aTinyShellScript/Polybar-Minibar-3D-Print-Files/Mods/MiniBar/[a]MB_Face_Plate.stl

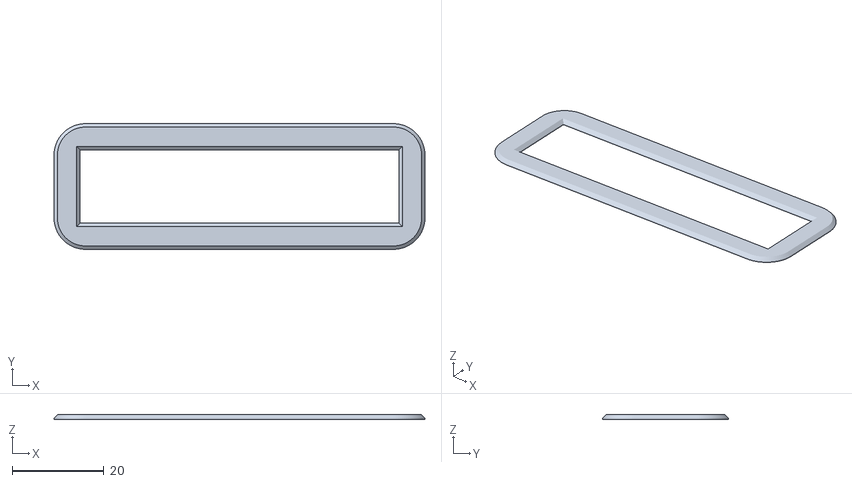
[picture p17: CAD file, 2022-12-14]
Mods/MiniBar/[a]MB_Face_Plate.stl
80.9 x 27.4 x 1.00
