aTinyShellScript/Polybar-Minibar-3D-Print-Files/Mods/PolyBar/[a]PB_Button_Board.stl

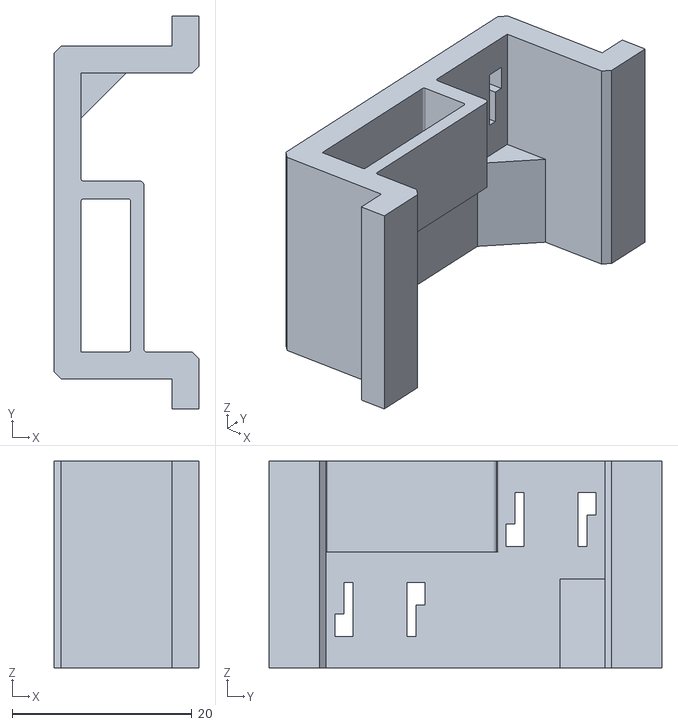
[picture p18: CAD file, 2022-12-14]
Mods/PolyBar/[a]PB_Button_Board.stl
16.1 x 43.7 x 23.0
