aTinyShellScript/Polybar-Minibar-3D-Print-Files/Mods/MiniBar/MB_Case_Top.stl

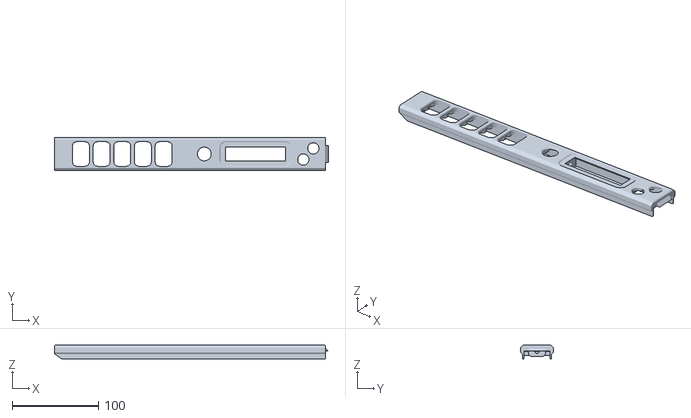
[picture p19: CAD file, 2022-12-14]
Mods/MiniBar/MB_Case_Top.stl
318.4 x 38.0 x 15.8
