aTinyShellScript/Polybar-Minibar-3D-Print-Files/Mods/PolyBar/[a]Strum_Swivel_Retainer_[x2].stl

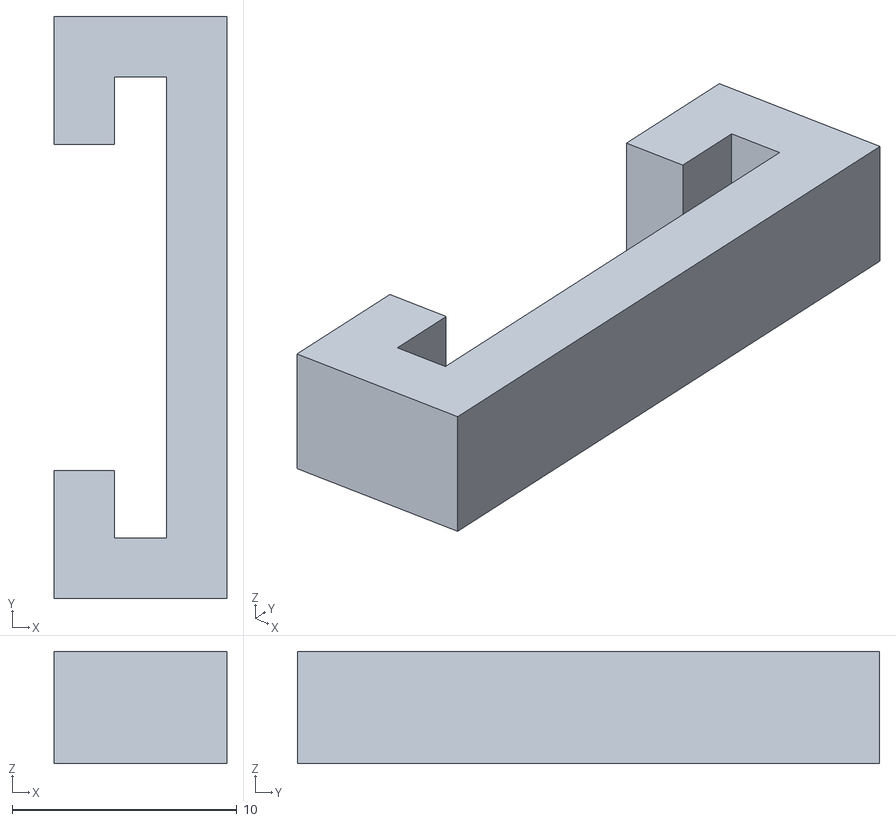
[picture p20: CAD file, 2022-12-14]
Mods/PolyBar/[a]Strum_Swivel_Retainer_[x2].stl
7.70 x 25.9 x 5.00
