aTinyShellScript/Polybar-Minibar-3D-Print-Files/Mods/MiniBar/MB_Strum_Bar.stl

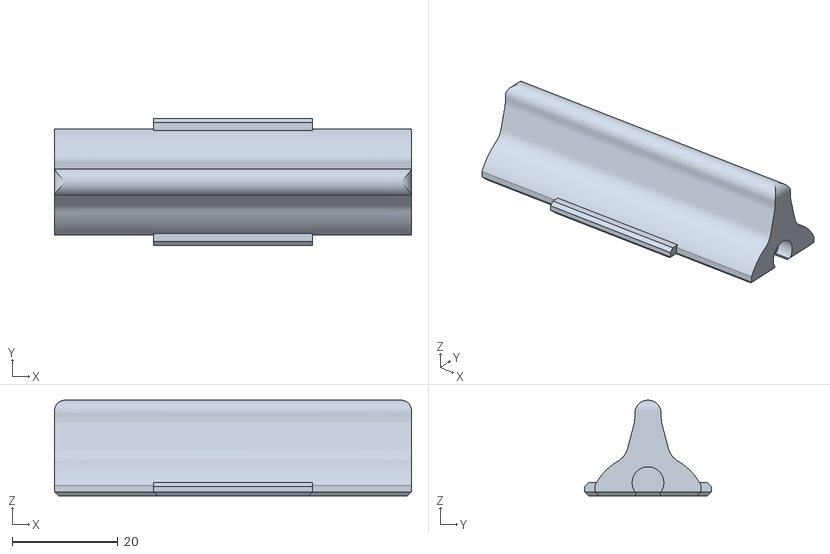
[picture p21: CAD file, 2022-12-14]
Mods/MiniBar/MB_Strum_Bar.stl
67.5 x 24.0 x 18.1
