aTinyShellScript/Polybar-Minibar-3D-Print-Files/Mods/PolyBar/[a]PB_Joystick_Board.stl

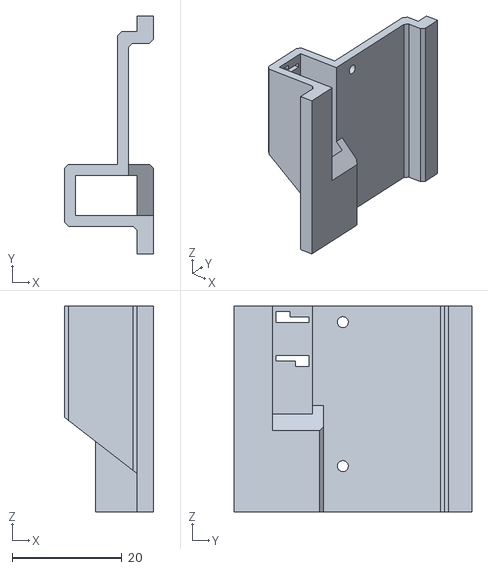
[picture p22: CAD file, 2022-12-14]
Mods/PolyBar/[a]PB_Joystick_Board.stl
16.2 x 43.4 x 37.5
