aTinyShellScript/Polybar-Minibar-3D-Print-Files/Mods/MiniBar/[a]MB_Small_Button_[x2].stl

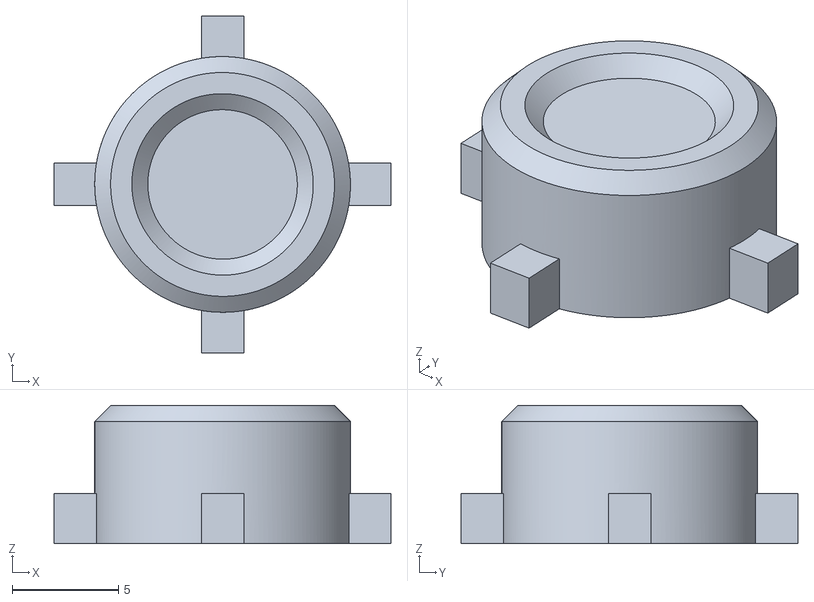
[picture p23: CAD file, 2022-12-14]
Mods/MiniBar/[a]MB_Small_Button_[x2].stl
15.9 x 15.9 x 6.50
