aTinyShellScript/Polybar-Minibar-3D-Print-Files/Mods/PolyBar/[a]Fret_Switches_Board.stl

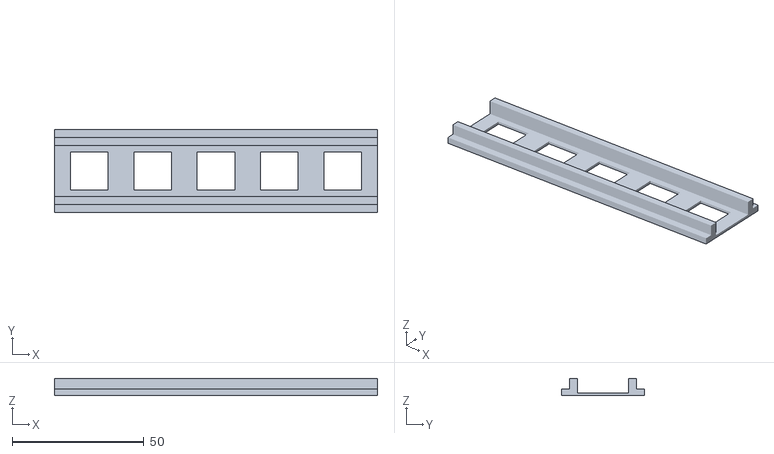
[picture p24: CAD file, 2022-12-14]
Mods/PolyBar/[a]Fret_Switches_Board.stl
122.5 x 31.5 x 6.60
