aTinyShellScript/Polybar-Minibar-3D-Print-Files/Mods/MiniBar/[a]Joystick_Cap.stl

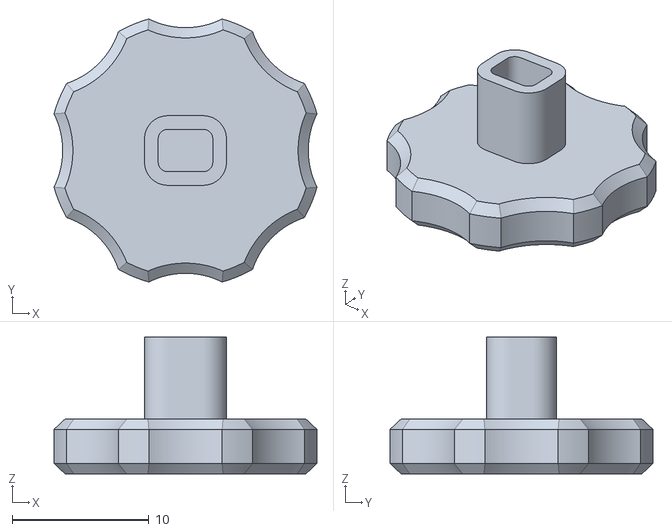
[picture p25: CAD file, 2022-12-14]
Mods/MiniBar/[a]Joystick_Cap.stl
19.3 x 19.3 x 10.00
