aTinyShellScript/Polybar-Minibar-3D-Print-Files/Mods/PolyBar/[a]Fret_Mount_Insert_[x5].stl

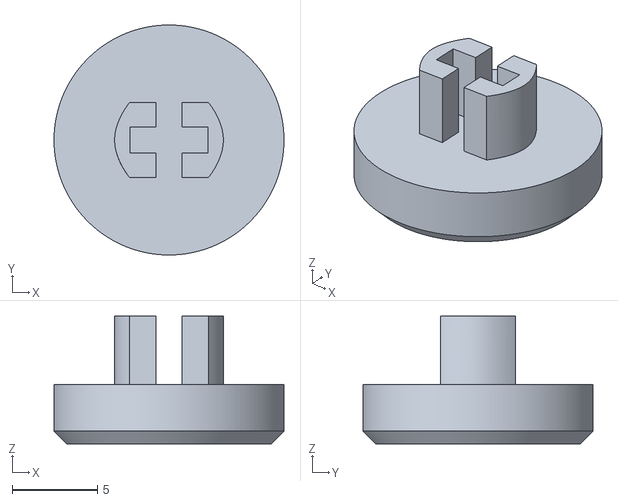
[picture p26: CAD file, 2022-12-14]
Mods/PolyBar/[a]Fret_Mount_Insert_[x5].stl
13.5 x 13.5 x 7.50
