aTinyShellScript/Polybar-Minibar-3D-Print-Files/Mods/MiniBar/[a]MB_Button_Board_Original_Height.stl

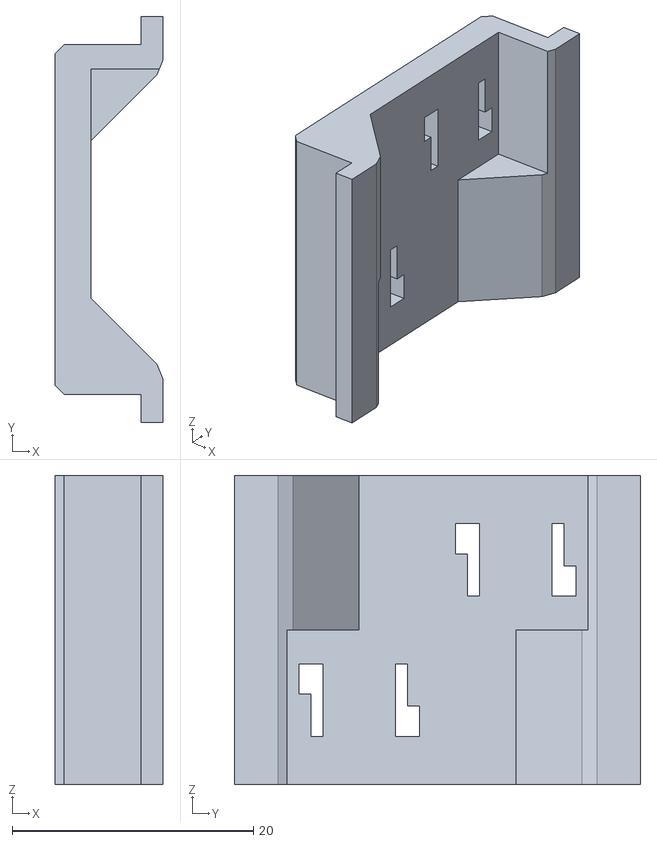
[picture p27: CAD file, 2022-12-14]
Mods/MiniBar/[a]MB_Button_Board_Original_Height.stl
8.98 x 33.7 x 25.6
