aTinyShellScript/Polybar-Minibar-3D-Print-Files/Mods/PolyBar/PB_Strum_Case_Top.stl

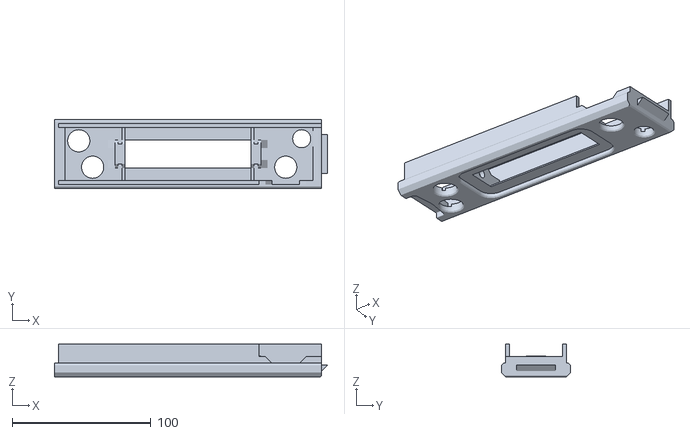
[picture p28: CAD file, 2022-12-14]
Mods/PolyBar/PB_Strum_Case_Top.stl
196.9 x 50.0 x 23.5
