aTinyShellScript/Polybar-Minibar-3D-Print-Files/Mods/MiniBar/[a]Board_Fret_Switches.stl

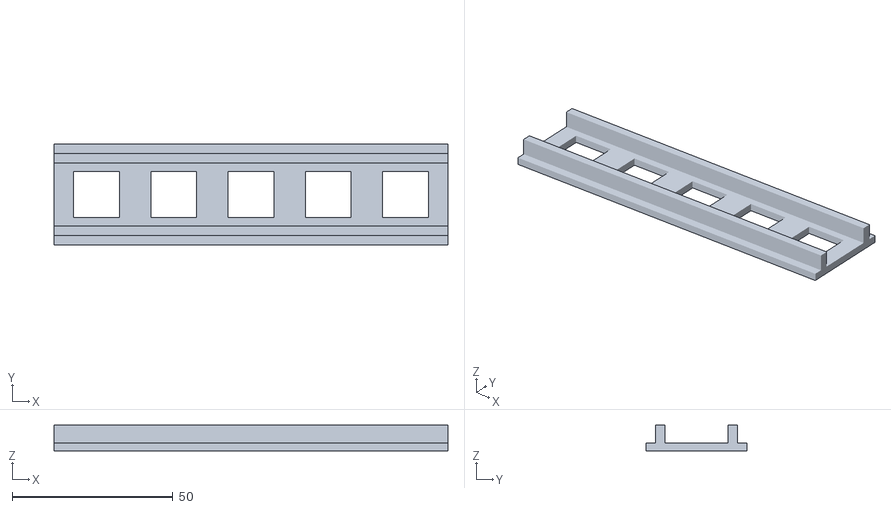
[picture p29: CAD file, 2022-12-14]
Mods/MiniBar/[a]Board_Fret_Switches.stl
122.5 x 31.5 x 8.00
