aTinyShellScript/Polybar-Minibar-3D-Print-Files/Mods/PolyBar/[a]PB_Large_Button_[x2].stl

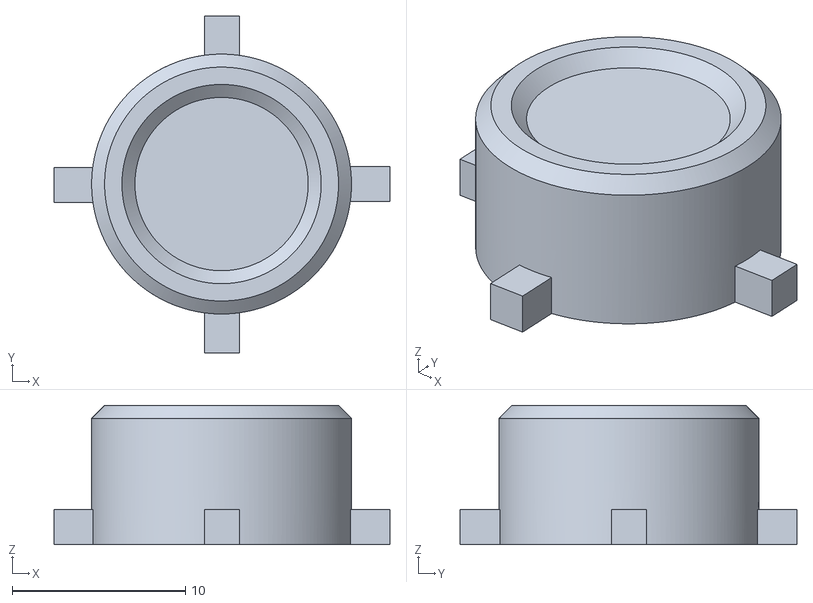
[picture p30: CAD file, 2022-12-14]
Mods/PolyBar/[a]PB_Large_Button_[x2].stl
19.4 x 19.4 x 8.04
