aTinyShellScript/Polybar-Minibar-3D-Print-Files/Mods/MiniBar/[a]MB_Strum_Board_[x2].stl

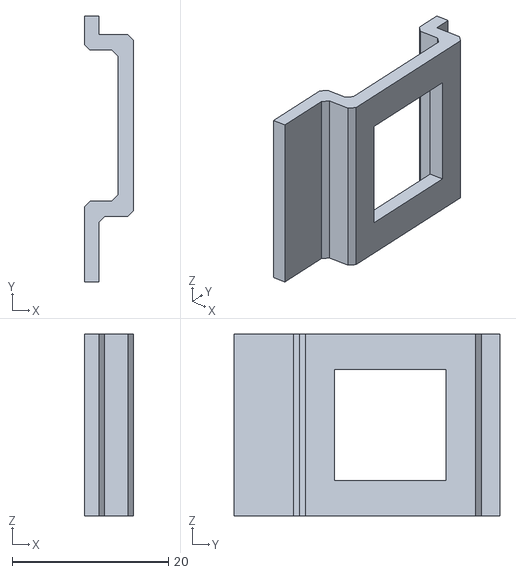
[picture p31: CAD file, 2022-12-14]
Mods/MiniBar/[a]MB_Strum_Board_[x2].stl
6.30 x 34.0 x 23.3
