aTinyShellScript/Polybar-Minibar-3D-Print-Files/Mods/PolyBar/PB_Fret_Extension_Bottom_SinglePiece.stl

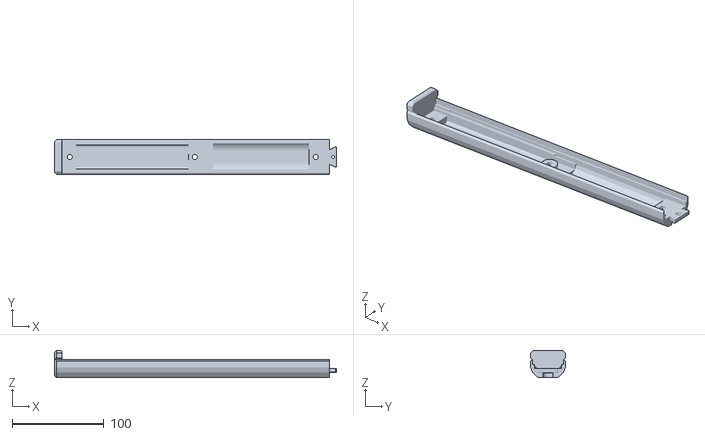
[picture p32: CAD file, 2022-12-14]
Mods/PolyBar/PB_Fret_Extension_Bottom_SinglePiece.stl
308.0 x 38.0 x 30.0
