aTinyShellScript/Polybar-Minibar-3D-Print-Files/Mods/PolyBar/[a]PB_Face_Plate.stl

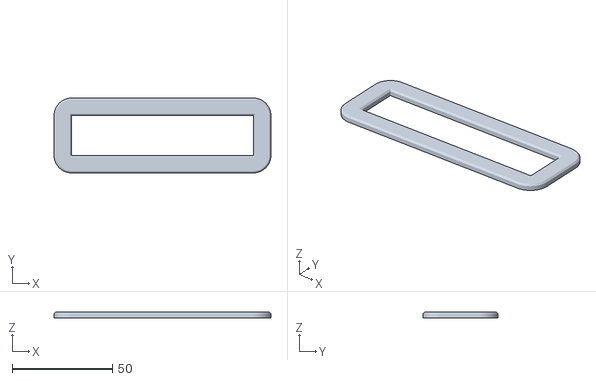
[picture p33: CAD file, 2022-12-14]
Mods/PolyBar/[a]PB_Face_Plate.stl
108.4 x 37.4 x 2.80
