aTinyShellScript/Polybar-Minibar-3D-Print-Files/Mods/PolyBar/[a]PB_Small_Button.stl

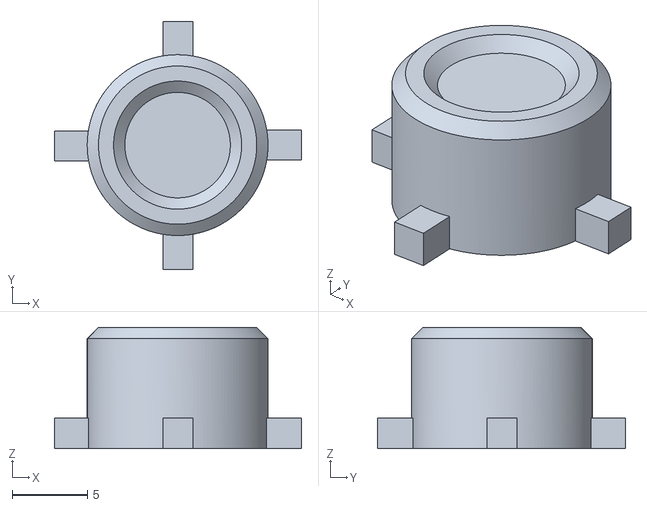
[picture p34: CAD file, 2022-12-14]
Mods/PolyBar/[a]PB_Small_Button.stl
16.4 x 16.4 x 8.04
