aTinyShellScript/Polybar-Minibar-3D-Print-Files/Mods/PolyBar/[a]PB_Strum_Board_[x2].stl

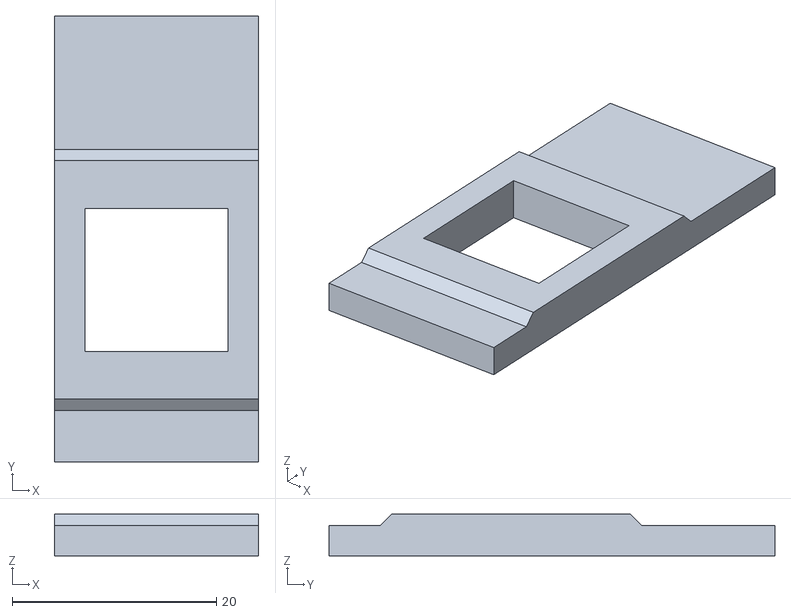
[picture p35: CAD file, 2022-12-14]
Mods/PolyBar/[a]PB_Strum_Board_[x2].stl
20.0 x 43.7 x 4.09
