aTinyShellScript/Polybar-Minibar-3D-Print-Files/Mods/PolyBar/PB_Fret_Extension_Top_SinglePiece.stl

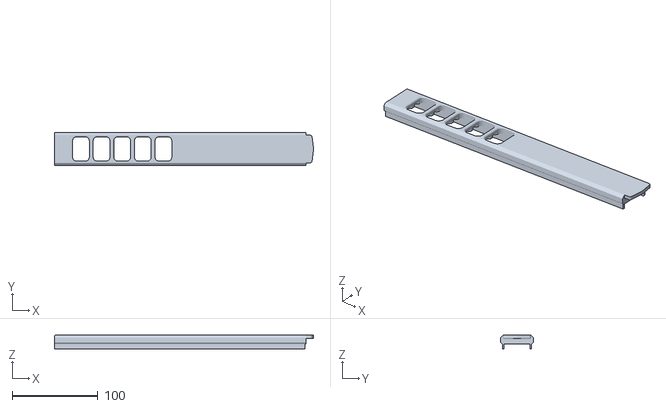
[picture p36: CAD file, 2022-12-14]
Mods/PolyBar/PB_Fret_Extension_Top_SinglePiece.stl
301.3 x 38.0 x 15.7
