aTinyShellScript/Polybar-Minibar-3D-Print-Files/Mods/MiniBar/[a]Strum_Switch_Insert_[x2].stl

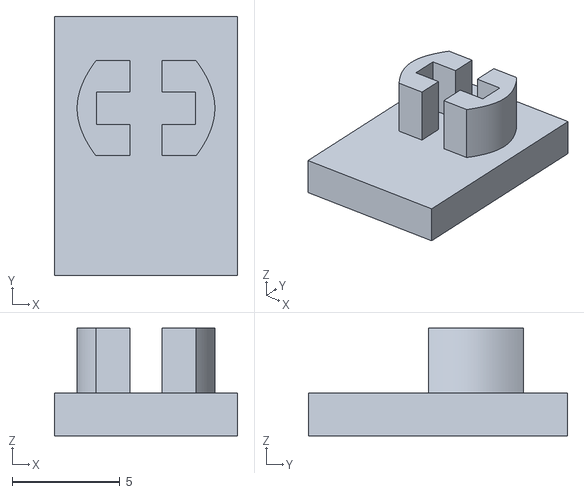
[picture p37: CAD file, 2022-12-14]
Mods/MiniBar/[a]Strum_Switch_Insert_[x2].stl
8.50 x 12.0 x 5.00
