aTinyShellScript/Polybar-Minibar-3D-Print-Files/Mods/PolyBar/PB_Strum_Case_Bottom.stl

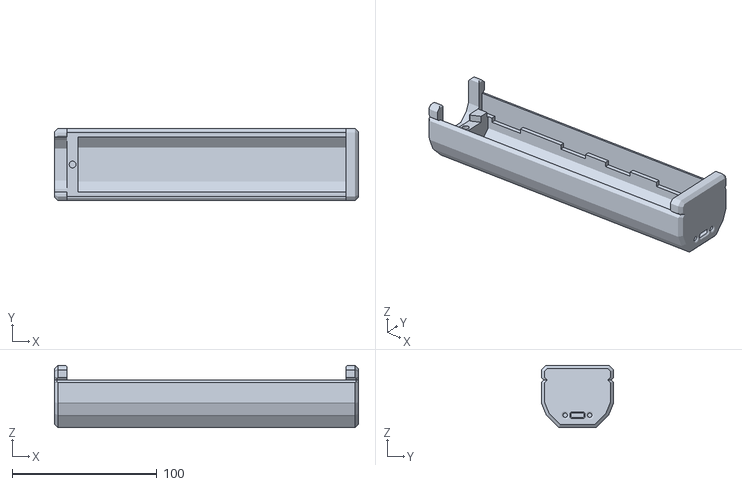
[picture p38: CAD file, 2022-12-14]
Mods/PolyBar/PB_Strum_Case_Bottom.stl
210.0 x 50.0 x 42.9
