aTinyShellScript/Polybar-Minibar-3D-Print-Files/Mods/PolyBar/[a]Joystick_Cap.stl

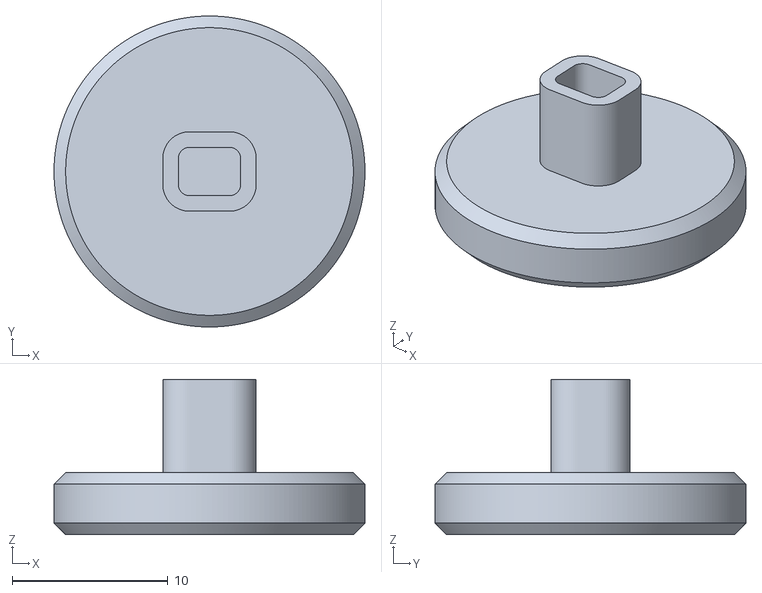
[picture p39: CAD file, 2022-12-14]
Mods/PolyBar/[a]Joystick_Cap.stl
20.0 x 20.0 x 10.0
